pauliano22/haven-dev-board-kicad/routing-evidence/images/C2.png

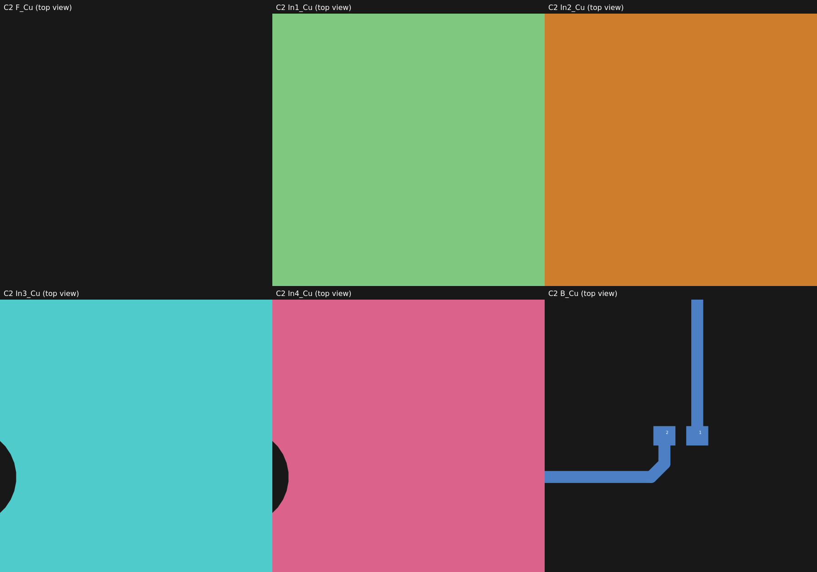
routing-evidence/images/C2.png
