pauliano22/haven-dev-board-kicad/routing-evidence/images/C6.png

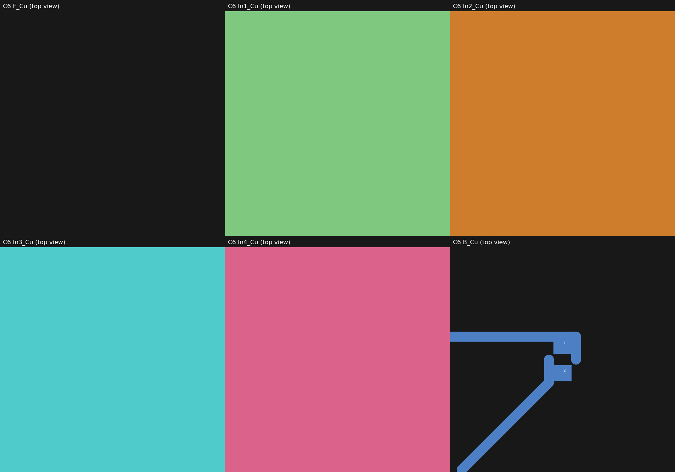
routing-evidence/images/C6.png
