pauliano22/haven-dev-board-kicad/routing-evidence/images/C9.png

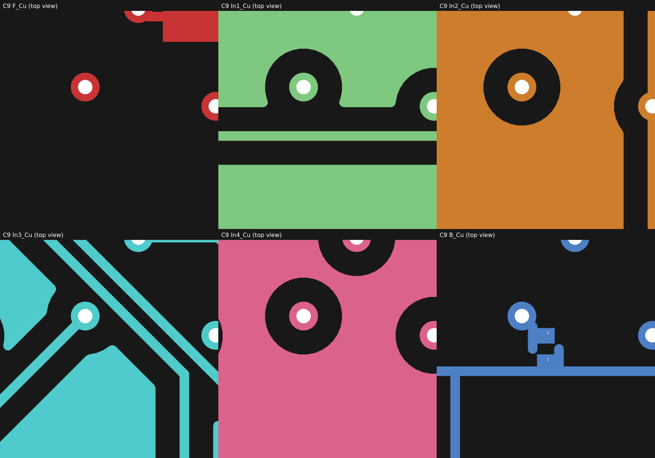
routing-evidence/images/C9.png
