pauliano22/haven-dev-board-kicad/routing-evidence/images/C19.png

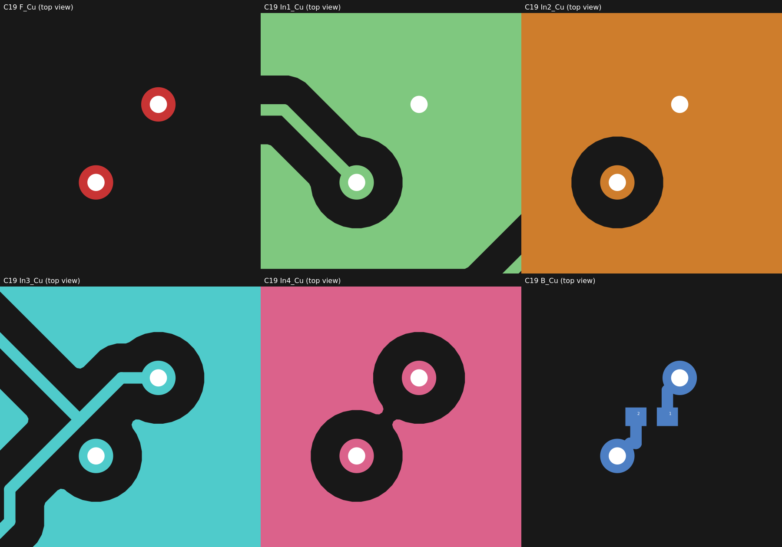
routing-evidence/images/C19.png
