pauliano22/haven-dev-board-kicad/routing-evidence/images/C22.png

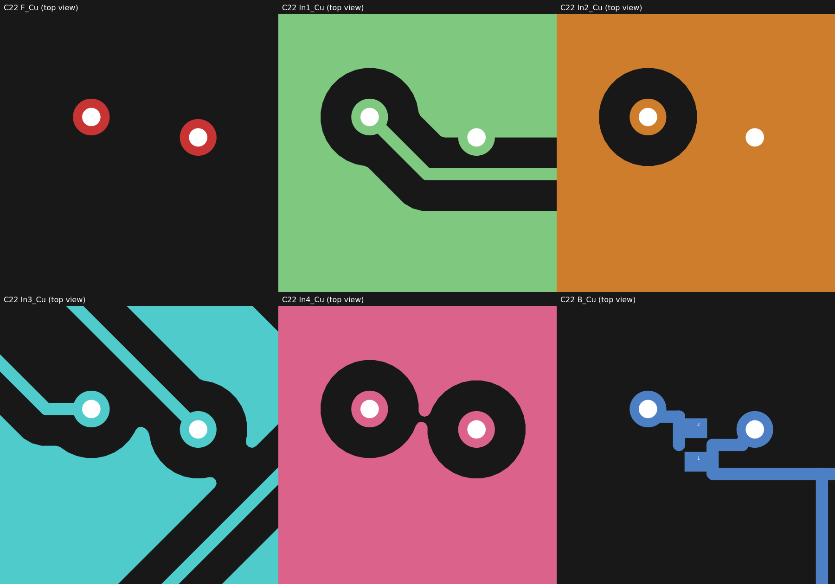
routing-evidence/images/C22.png
