pauliano22/haven-dev-board-kicad/routing-evidence/images/C32.png

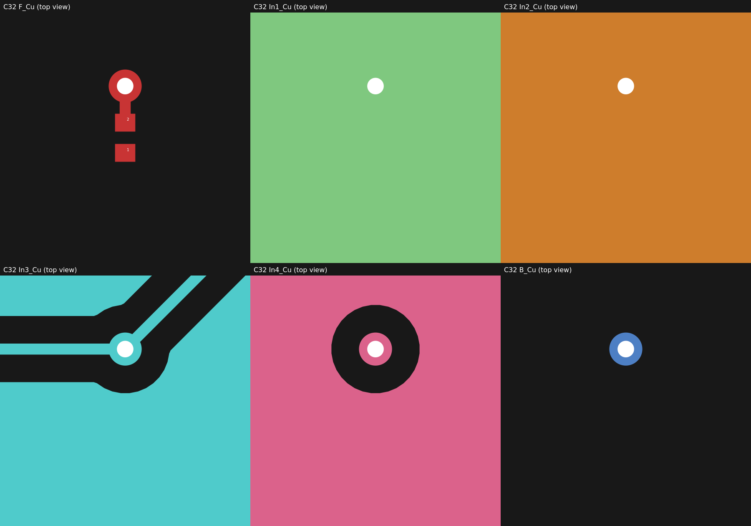
routing-evidence/images/C32.png
