pauliano22/haven-dev-board-kicad/routing-evidence/images/C34.png

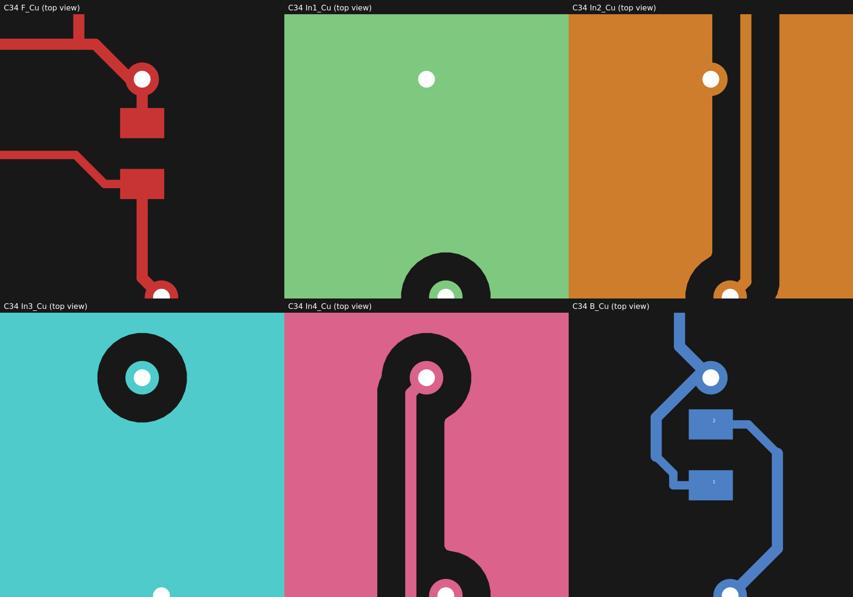
routing-evidence/images/C34.png
