pauliano22/haven-dev-board-kicad/routing-evidence/images/C36.png

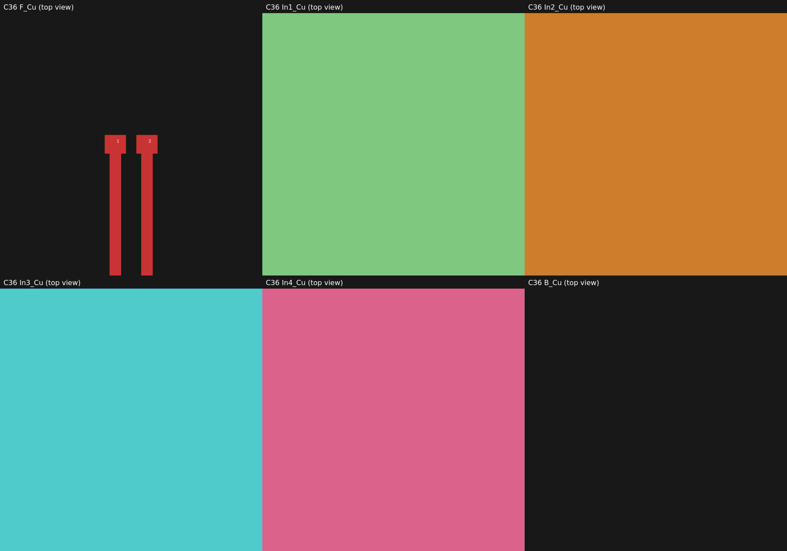
routing-evidence/images/C36.png
