pauliano22/haven-dev-board-kicad/routing-evidence/images/C38.png

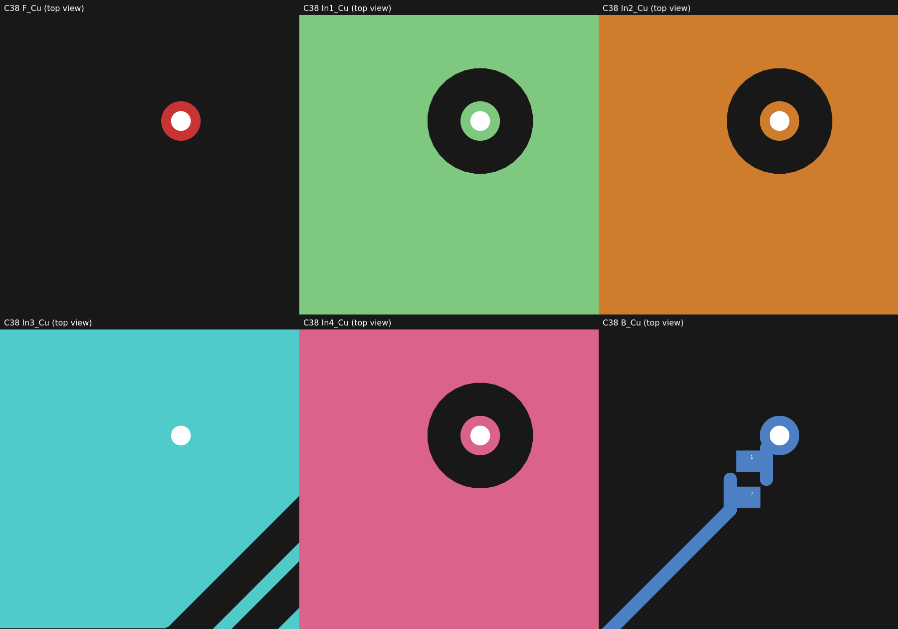
routing-evidence/images/C38.png
