pauliano22/haven-dev-board-kicad/routing-evidence/images/C46.png

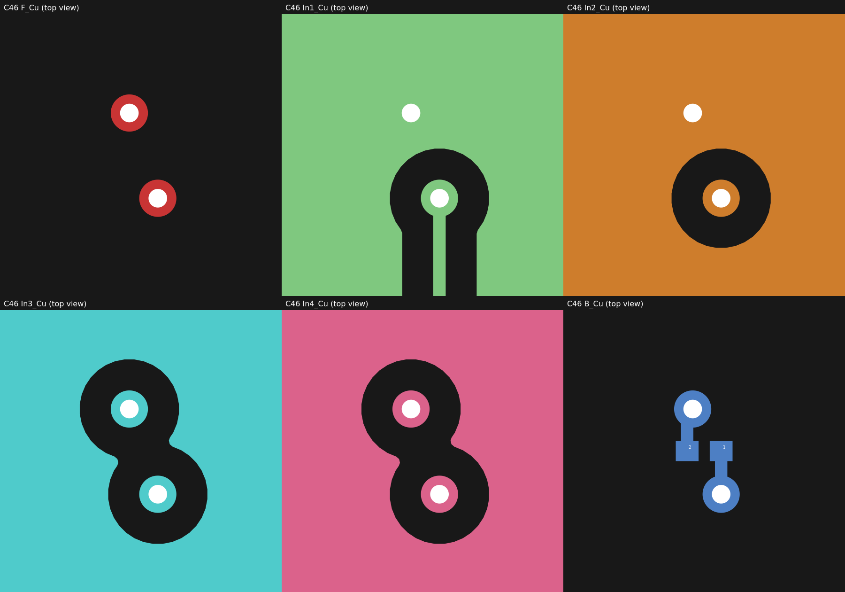
routing-evidence/images/C46.png
