pauliano22/haven-dev-board-kicad/routing-evidence/images/CN1.png

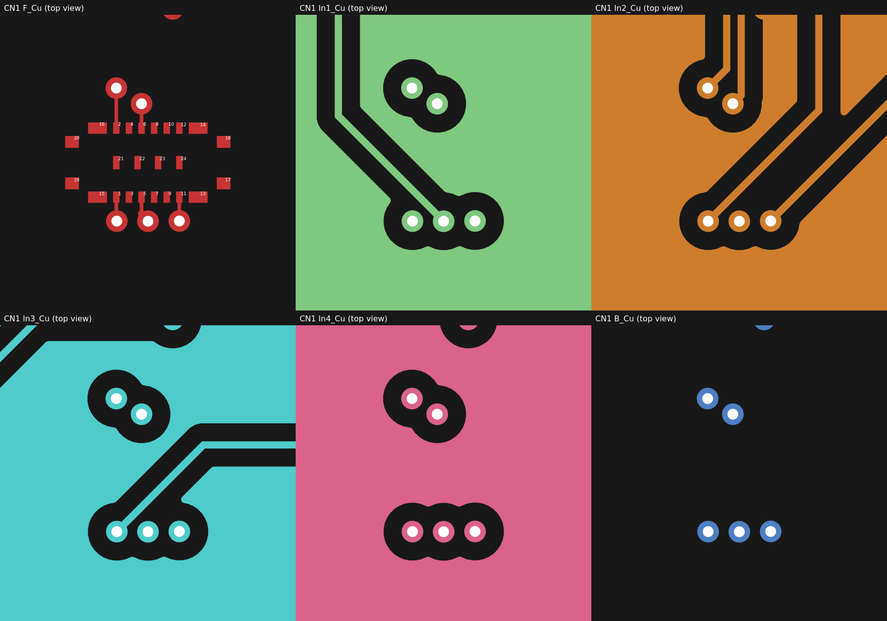
routing-evidence/images/CN1.png
