pauliano22/haven-dev-board-kicad/routing-evidence/images/U2.png

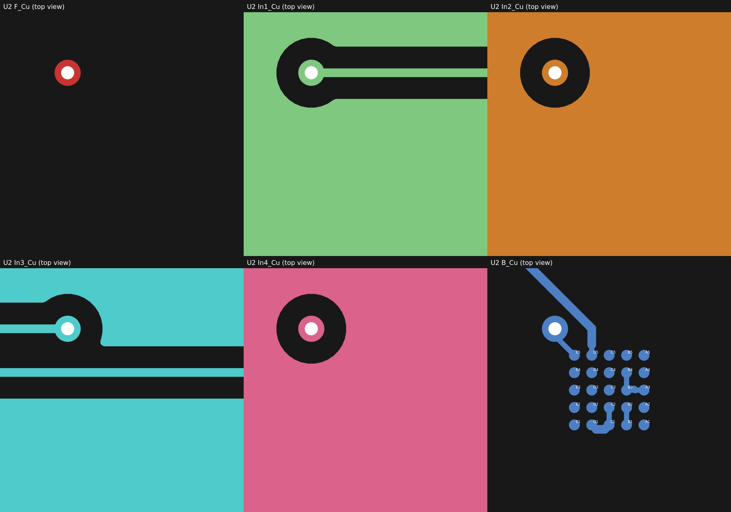
routing-evidence/images/U2.png
