pauliano22/haven-dev-board-kicad/routing-evidence/images/U10.png

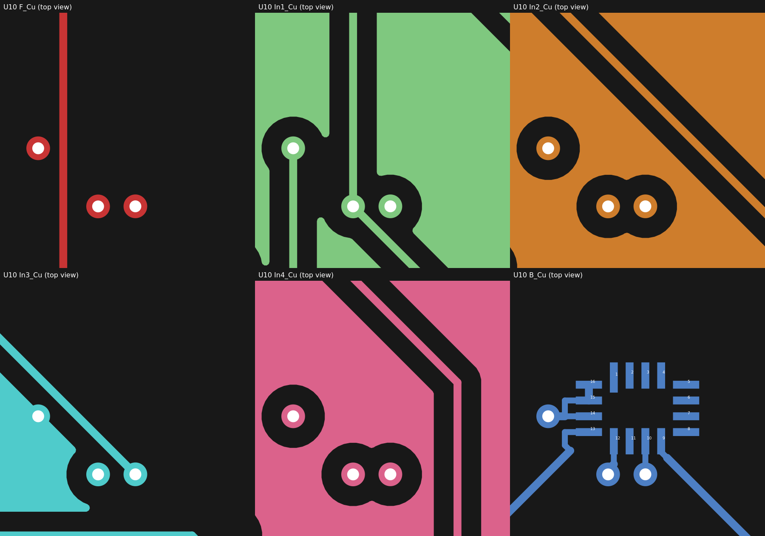
routing-evidence/images/U10.png
