pauliano22/haven-dev-board-kicad/routing-evidence/images/U15.png

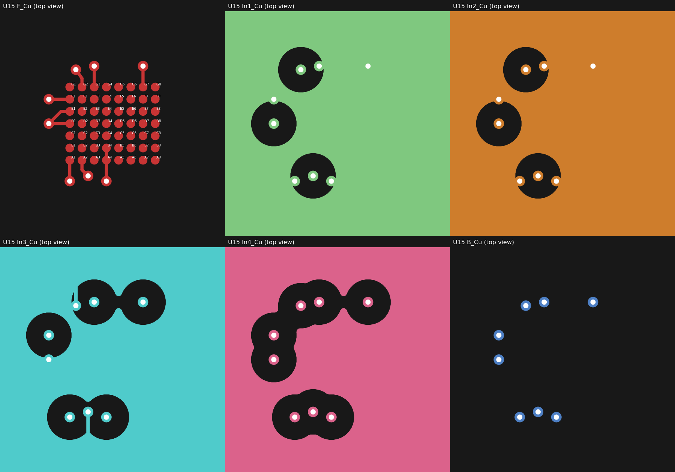
routing-evidence/images/U15.png
