pauliano22/haven-dev-board-kicad/routing-evidence/session4/C9-final.png

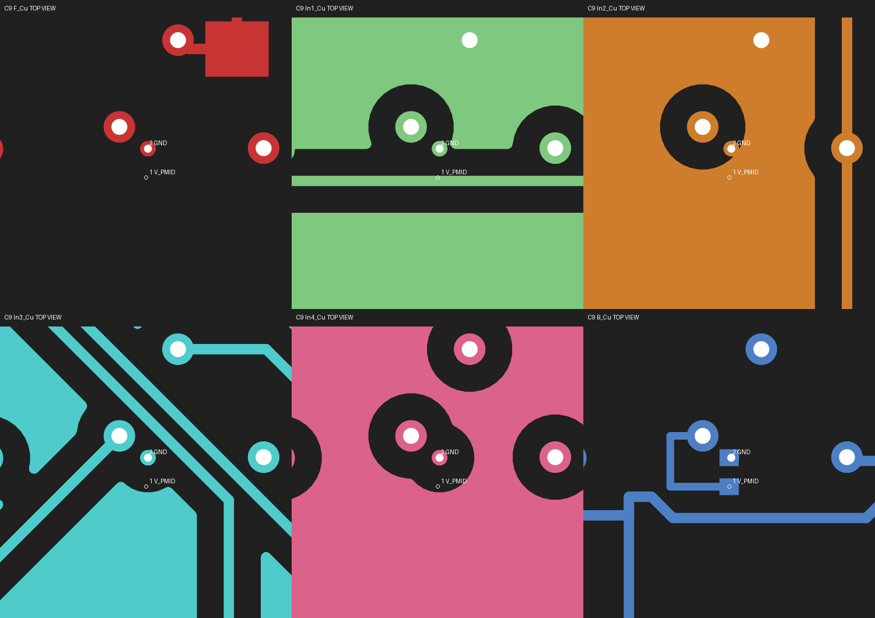
routing-evidence/session4/C9-final.png
