pauliano22/haven-dev-board-kicad/routing-evidence/session4/C22.png

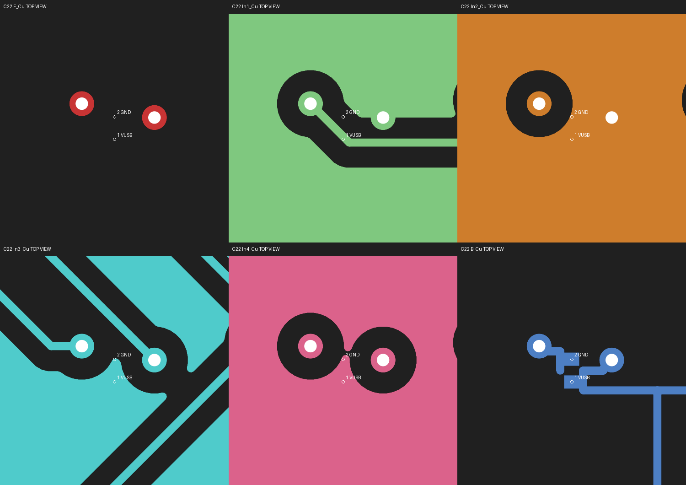
routing-evidence/session4/C22.png
