pauliano22/haven-dev-board-kicad/routing-evidence/session4/C38-final.png

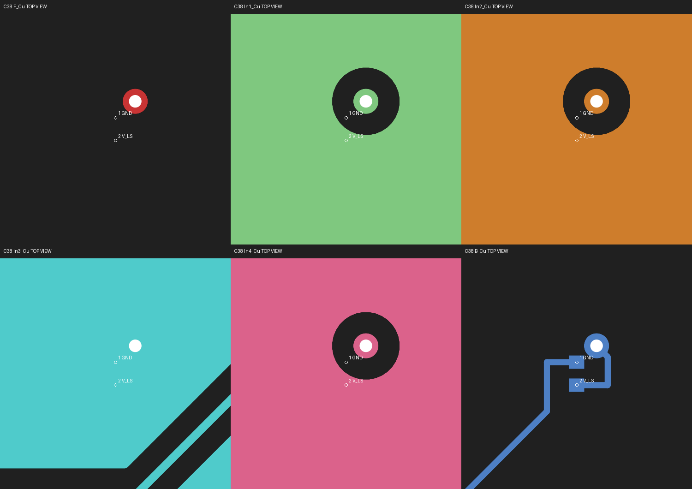
routing-evidence/session4/C38-final.png
