pauliano22/haven-dev-board-kicad/routing-evidence/session4/C44-final.png

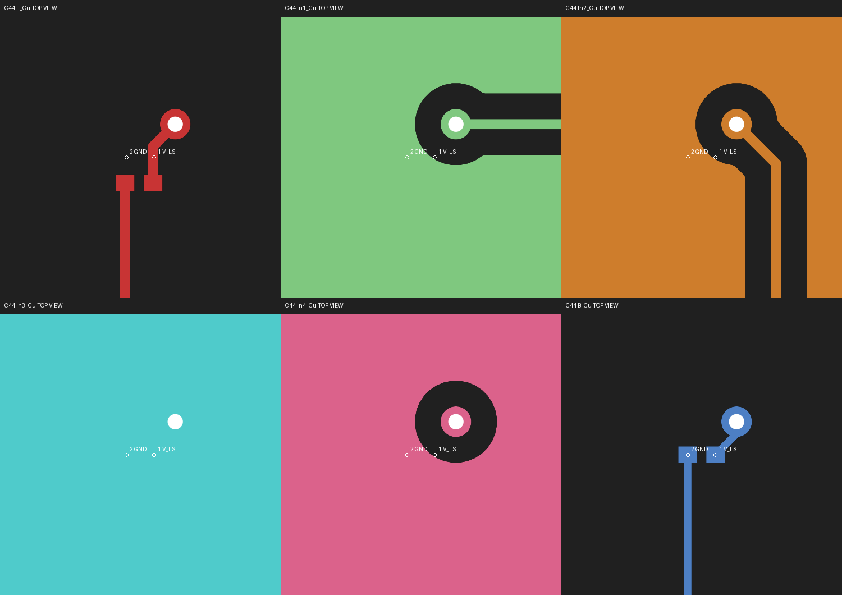
routing-evidence/session4/C44-final.png
