pauliano22/haven-dev-board-kicad/routing-evidence/session5/C23-final.png

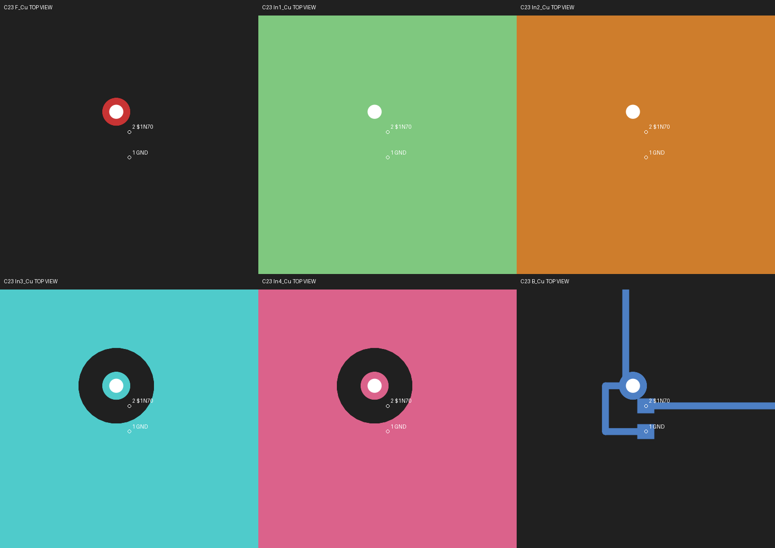
routing-evidence/session5/C23-final.png
