pauliano22/haven-dev-board-kicad/routing-evidence/session5/R6-final.png

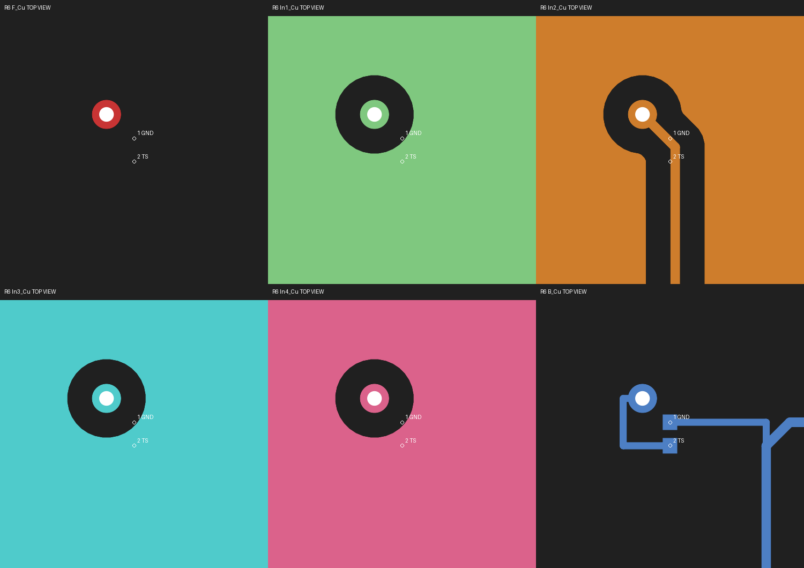
routing-evidence/session5/R6-final.png
