pauliano22/haven-dev-board-kicad/routing-evidence/session5/R13-final.png

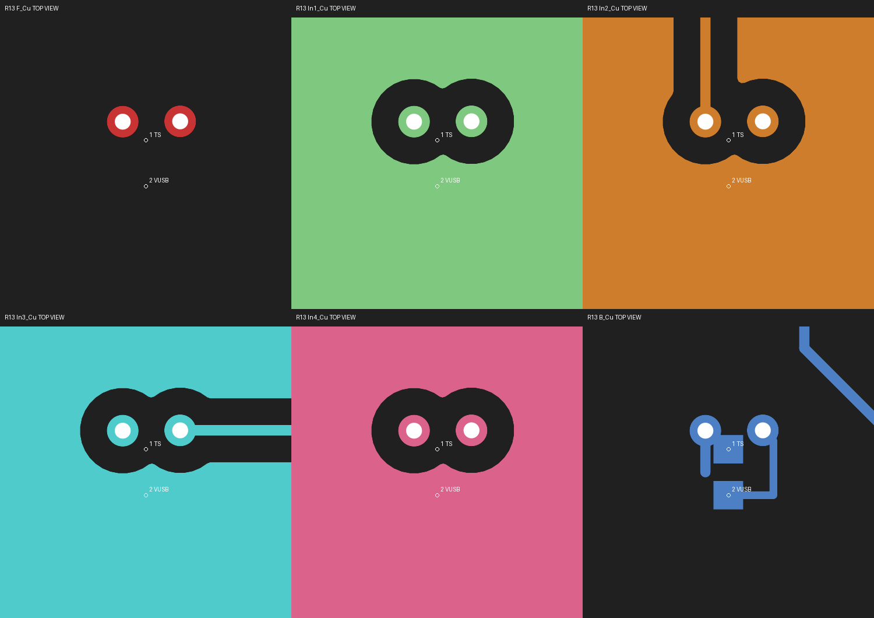
routing-evidence/session5/R13-final.png
