pauliano22/haven-dev-board-kicad/routing-evidence/session4/final-bottom-montage.png

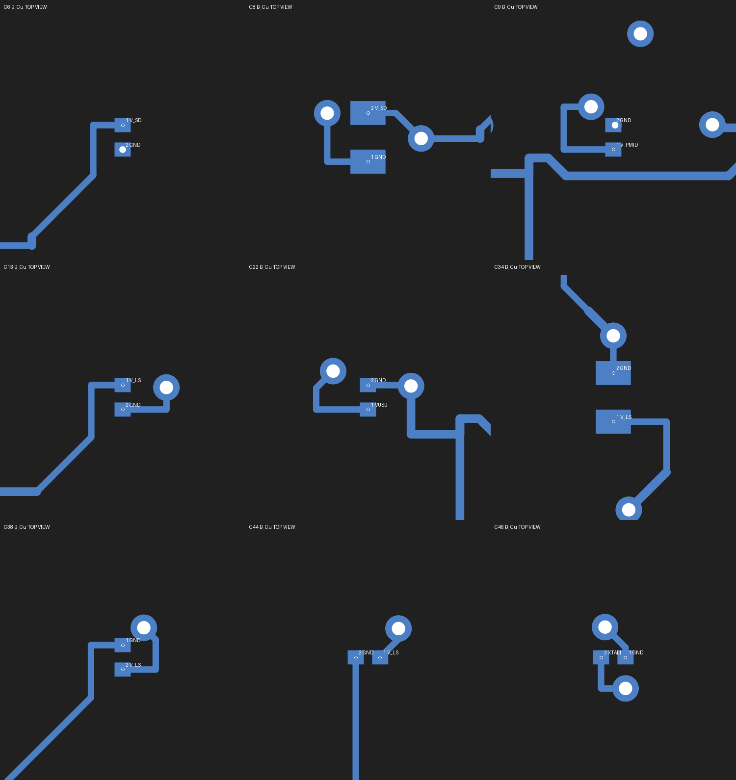
routing-evidence/session4/final-bottom-montage.png
